linkin-parks-bassist/kestrel-pcb/3dmodels/neutrik-nmj4hcd2/NMJ4HCD2.png

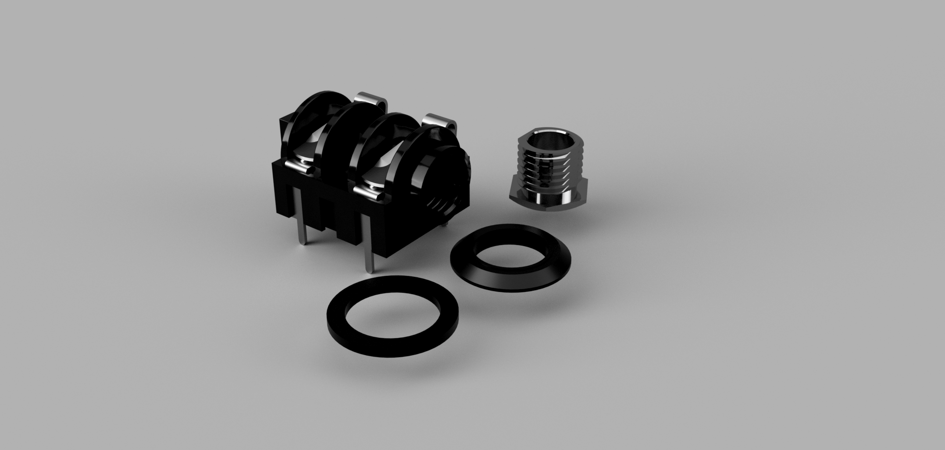
3dmodels/neutrik-nmj4hcd2/NMJ4HCD2.png
