linkin-parks-bassist/kestrel-pcb/rev-b/generated/pcb-adc-power.png

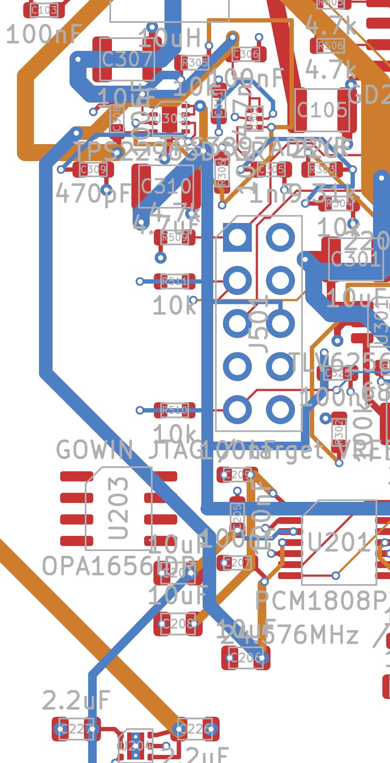
rev-b/generated/pcb-adc-power.png
