linkin-parks-bassist/kestrel-pcb/rev-b/generated/pcb-adc-support.png

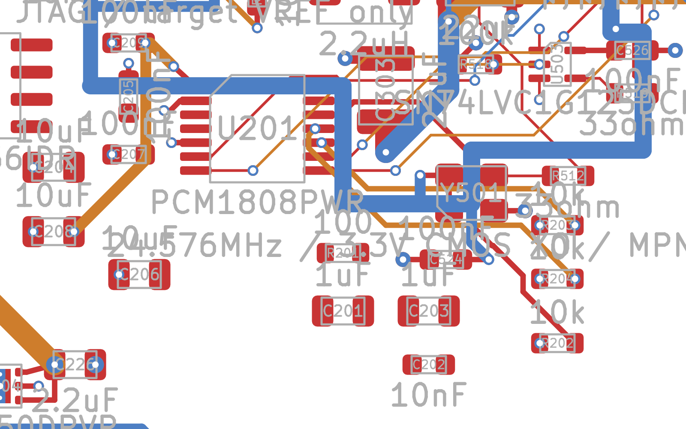
rev-b/generated/pcb-adc-support.png
