linkin-parks-bassist/kestrel-pcb/rev-b/generated/pcb-analogue-input.png

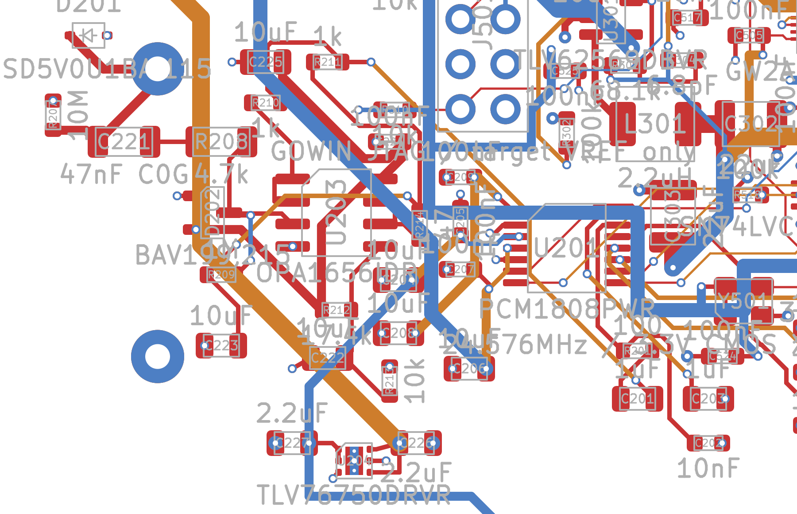
rev-b/generated/pcb-analogue-input.png
