linkin-parks-bassist/kestrel-pcb/rev-b/generated/pcb-analogue-output.png

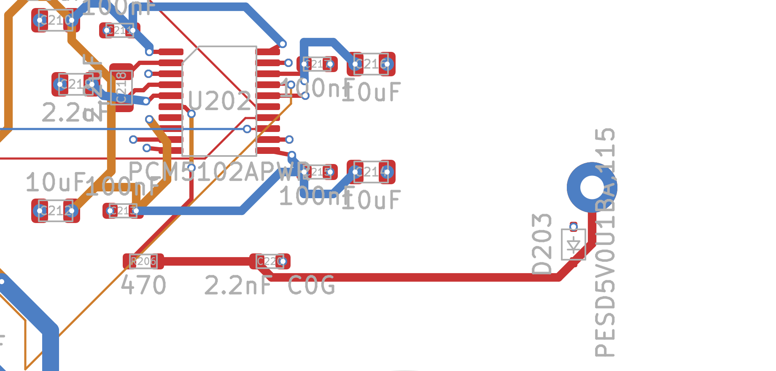
rev-b/generated/pcb-analogue-output.png
