linkin-parks-bassist/kestrel-pcb/rev-b/generated/pcb-analogue-power.png

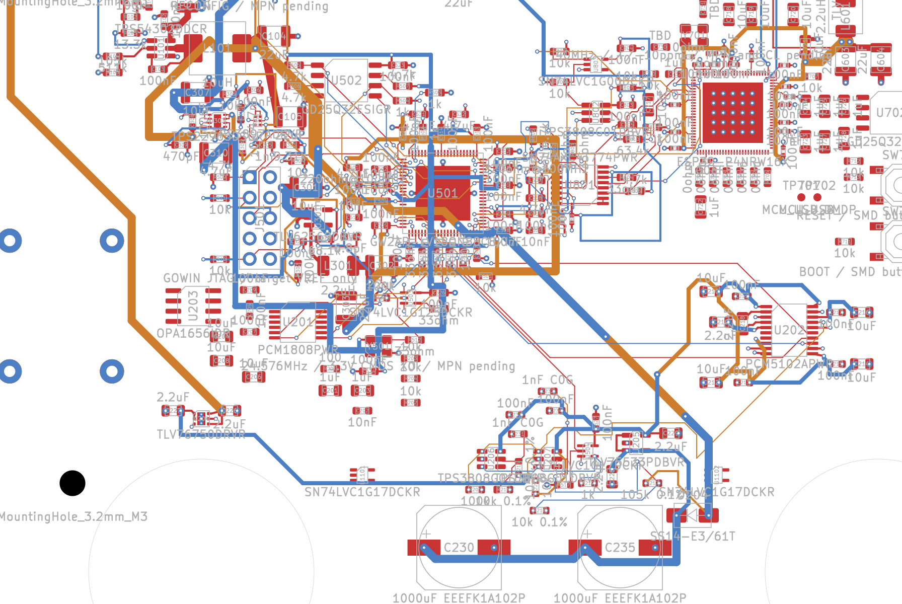
rev-b/generated/pcb-analogue-power.png
