linkin-parks-bassist/kestrel-pcb/rev-b/generated/pcb-audio-mute.png

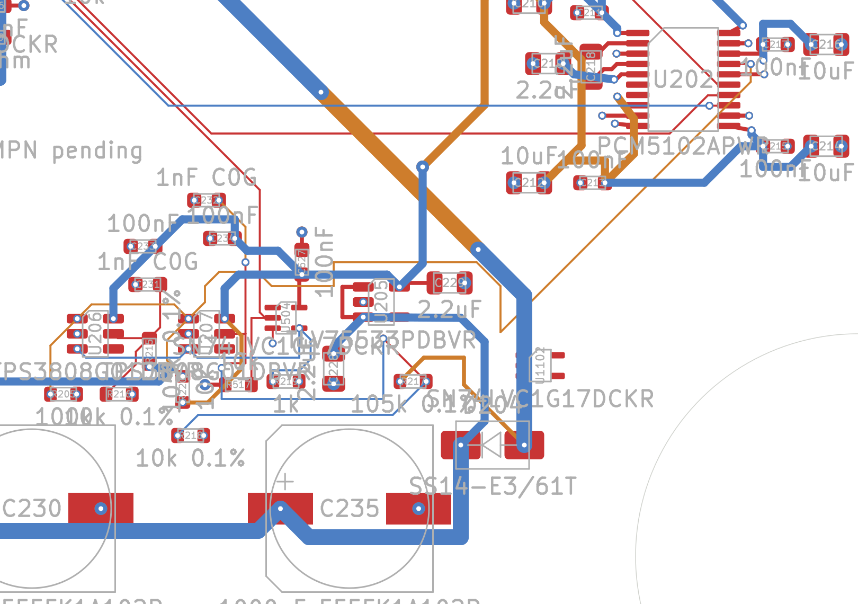
rev-b/generated/pcb-audio-mute.png
