linkin-parks-bassist/kestrel-pcb/rev-b/generated/pcb-backlight-pwm-escape.png

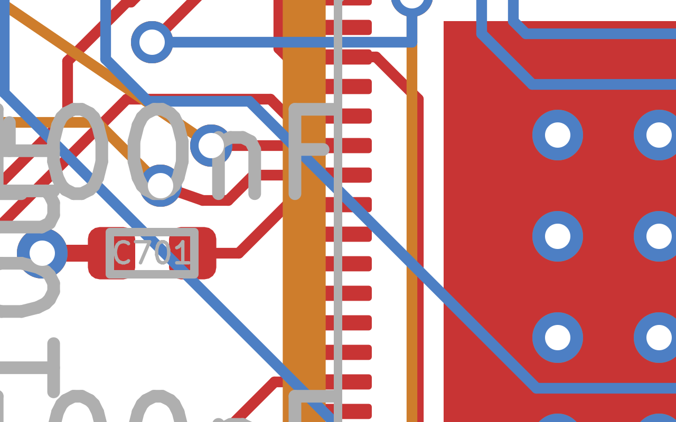
rev-b/generated/pcb-backlight-pwm-escape.png
