linkin-parks-bassist/kestrel-pcb/rev-b/generated/pcb-backlight-supply.png

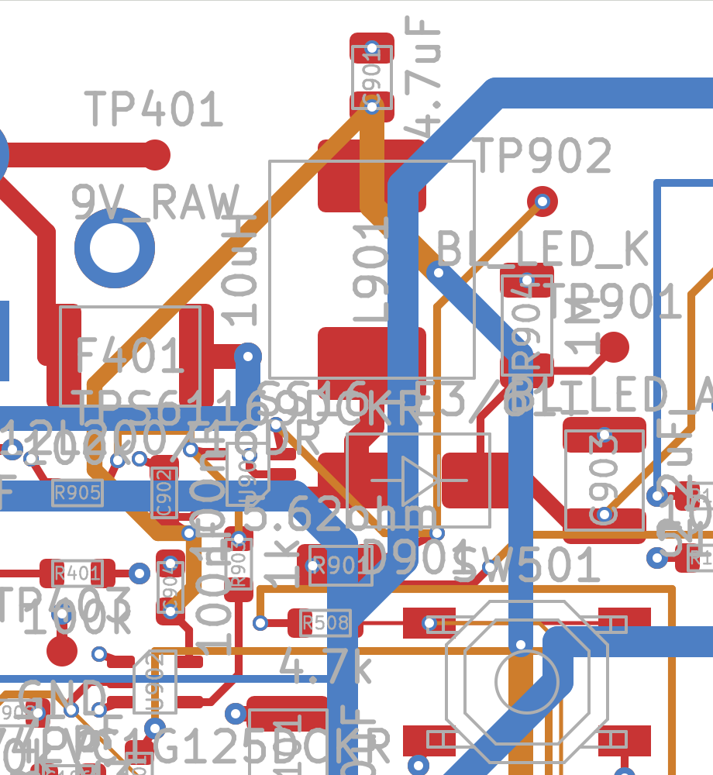
rev-b/generated/pcb-backlight-supply.png
