linkin-parks-bassist/kestrel-pcb/rev-b/generated/pcb-dac-support.png

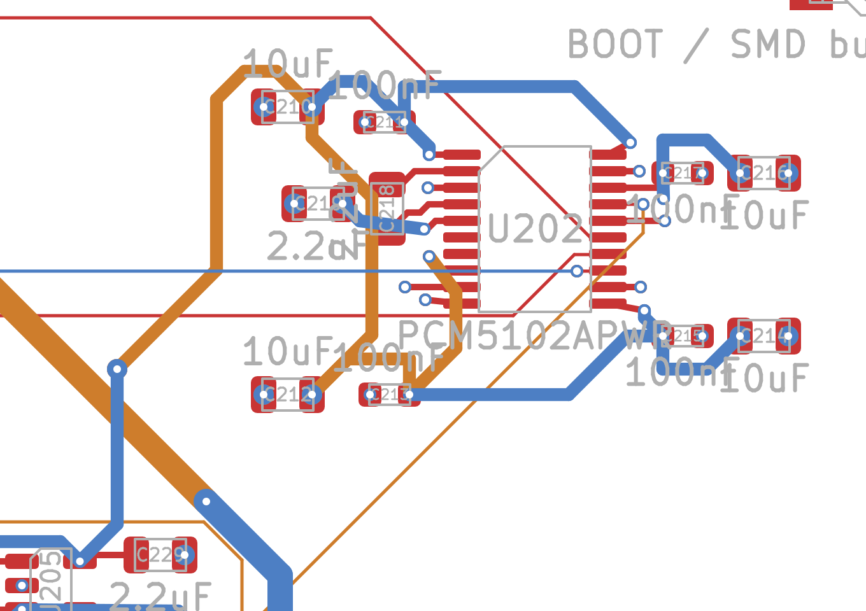
rev-b/generated/pcb-dac-support.png
