linkin-parks-bassist/kestrel-pcb/rev-b/generated/pcb-display-connector-supply.png

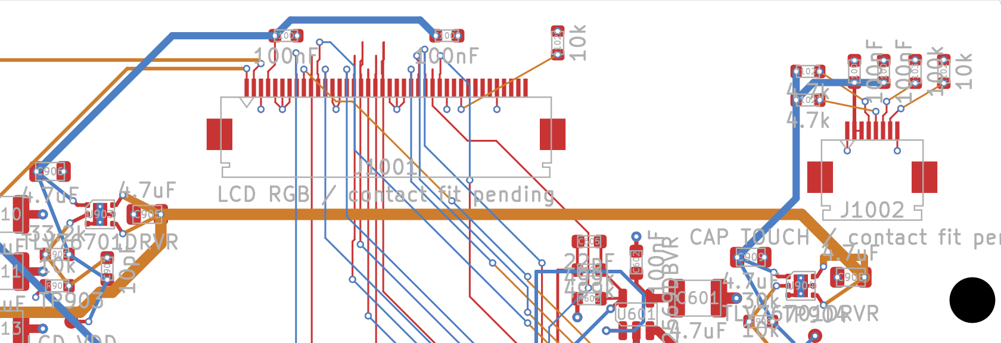
rev-b/generated/pcb-display-connector-supply.png
