linkin-parks-bassist/kestrel-pcb/rev-b/generated/pcb-display-feeds.png

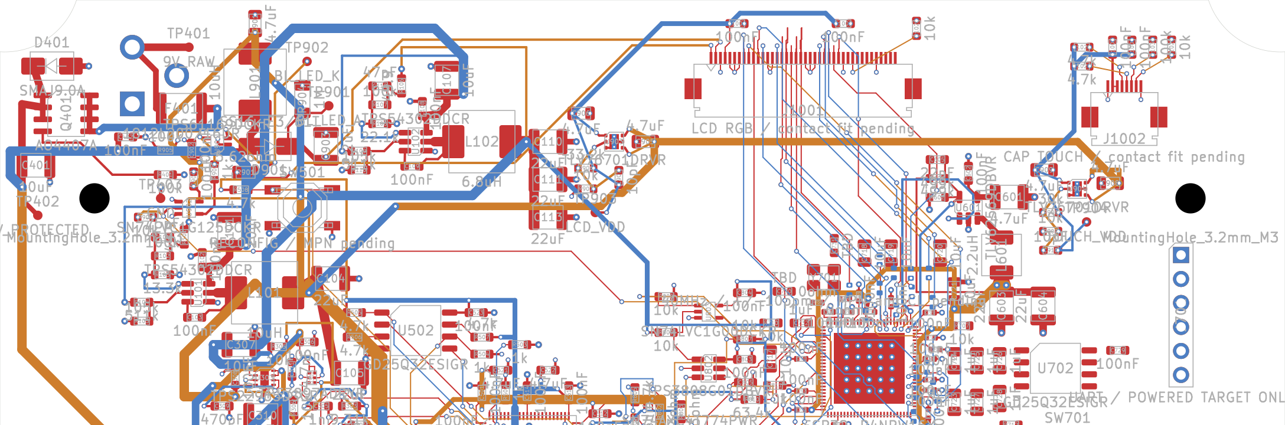
rev-b/generated/pcb-display-feeds.png
