linkin-parks-bassist/kestrel-pcb/rev-b/generated/pcb-display-led-fpc.png

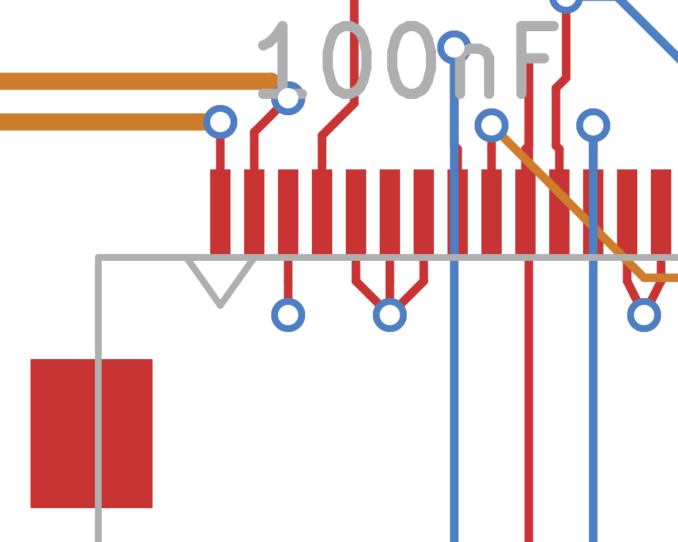
rev-b/generated/pcb-display-led-fpc.png
