linkin-parks-bassist/kestrel-pcb/rev-b/generated/pcb-display-rgb-damping.png

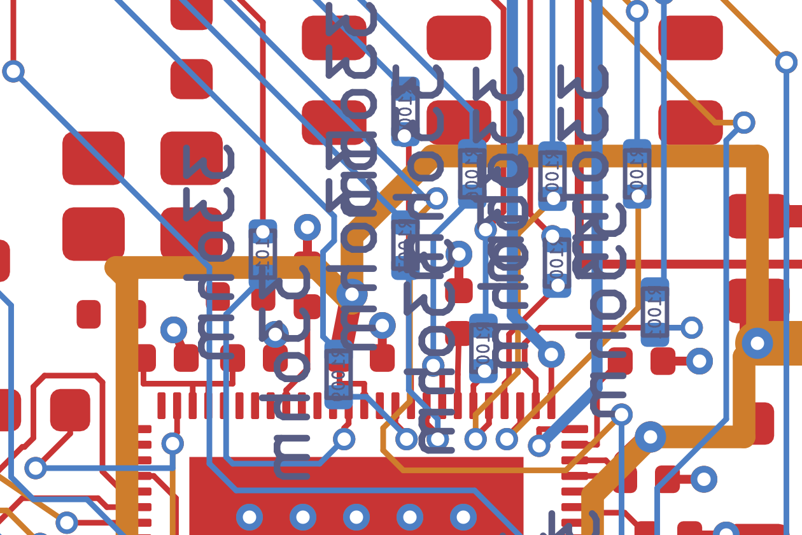
rev-b/generated/pcb-display-rgb-damping.png
