linkin-parks-bassist/kestrel-pcb/rev-b/generated/pcb-display-rgb-output-escape.png

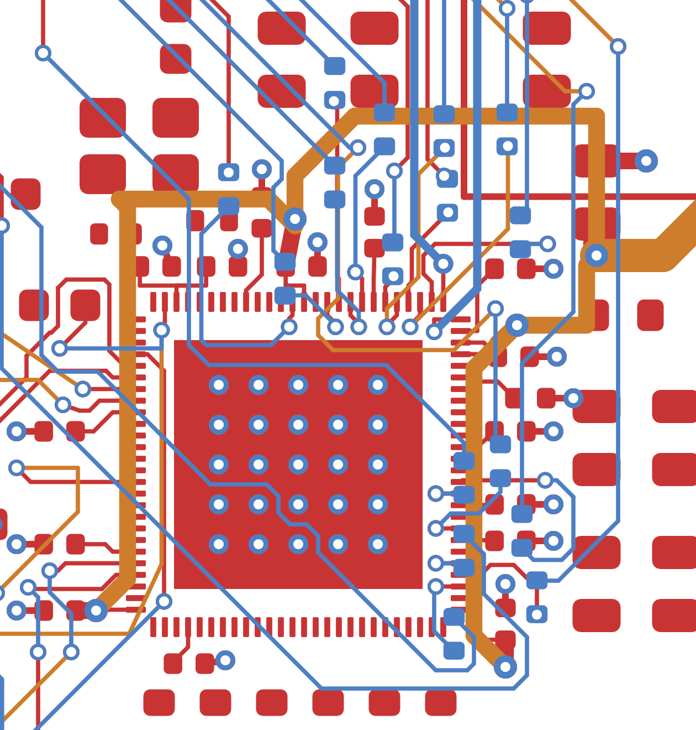
rev-b/generated/pcb-display-rgb-output-escape.png
