linkin-parks-bassist/kestrel-pcb/rev-b/generated/pcb-display-rgb-output.png

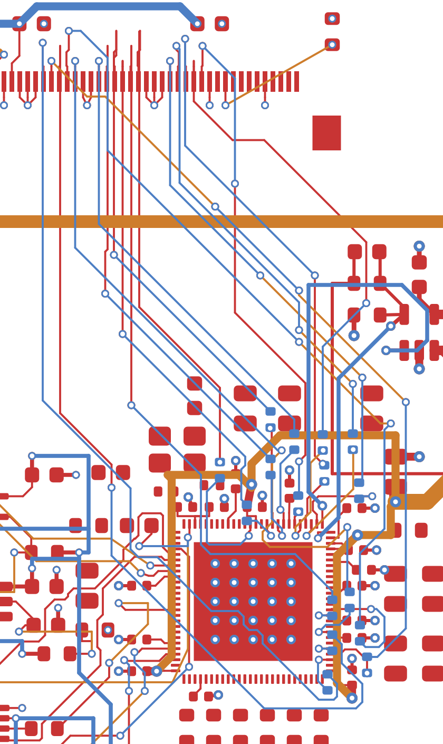
rev-b/generated/pcb-display-rgb-output.png
