linkin-parks-bassist/kestrel-pcb/rev-b/generated/pcb-display-rgb-right.png

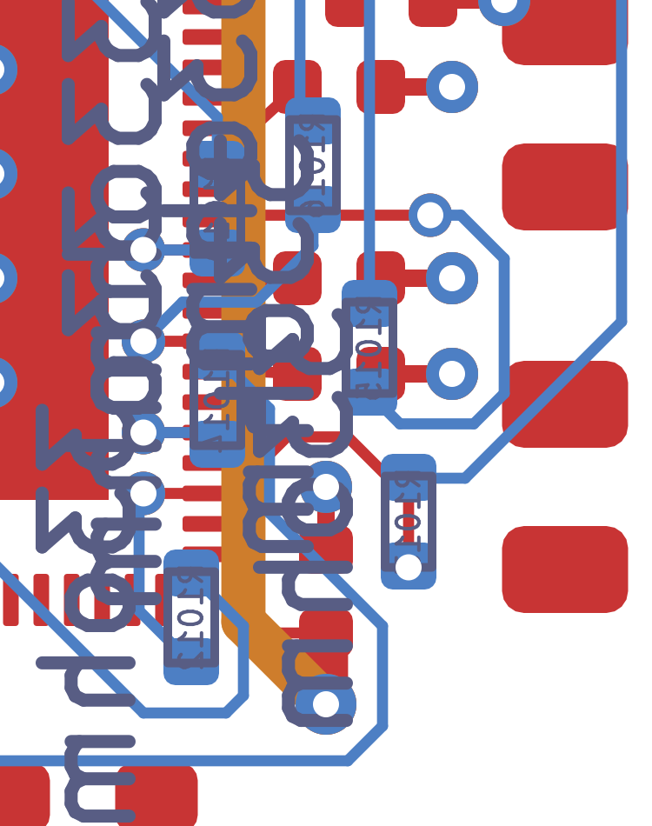
rev-b/generated/pcb-display-rgb-right.png
