linkin-parks-bassist/kestrel-pcb/rev-b/generated/pcb-footswitch-left.png

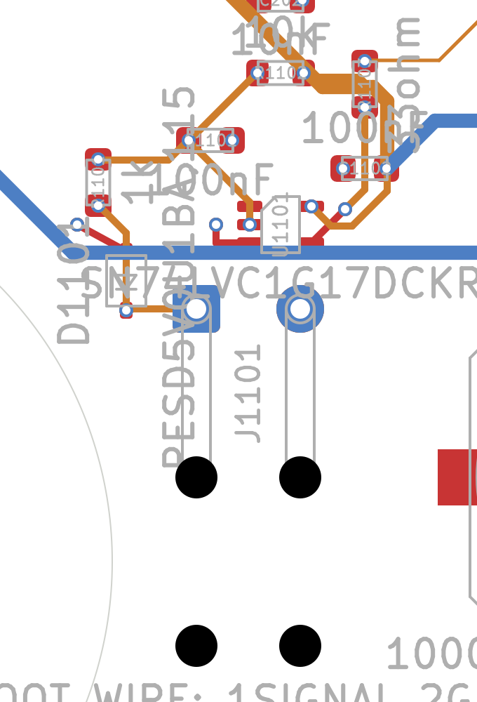
rev-b/generated/pcb-footswitch-left.png
