linkin-parks-bassist/kestrel-pcb/rev-b/generated/pcb-footswitch-mcu.png

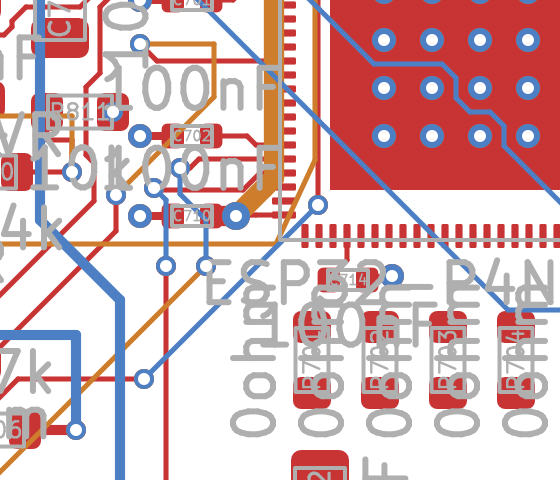
rev-b/generated/pcb-footswitch-mcu.png
