linkin-parks-bassist/kestrel-pcb/rev-b/generated/pcb-footswitch-placement.png

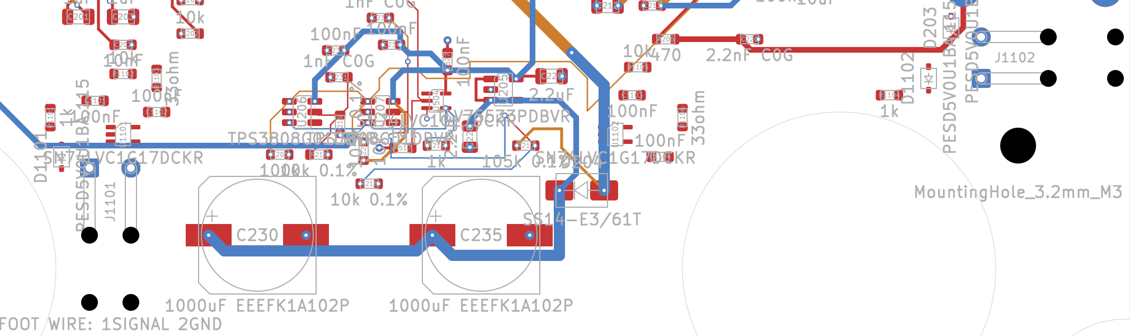
rev-b/generated/pcb-footswitch-placement.png
