linkin-parks-bassist/kestrel-pcb/rev-b/generated/pcb-footswitch-right.png

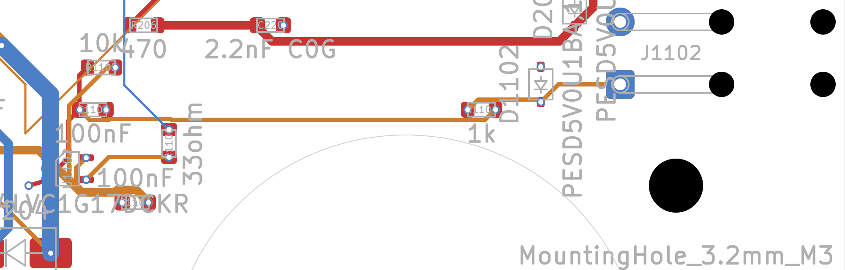
rev-b/generated/pcb-footswitch-right.png
