linkin-parks-bassist/kestrel-pcb/rev-b/generated/pcb-fpga-audio.png

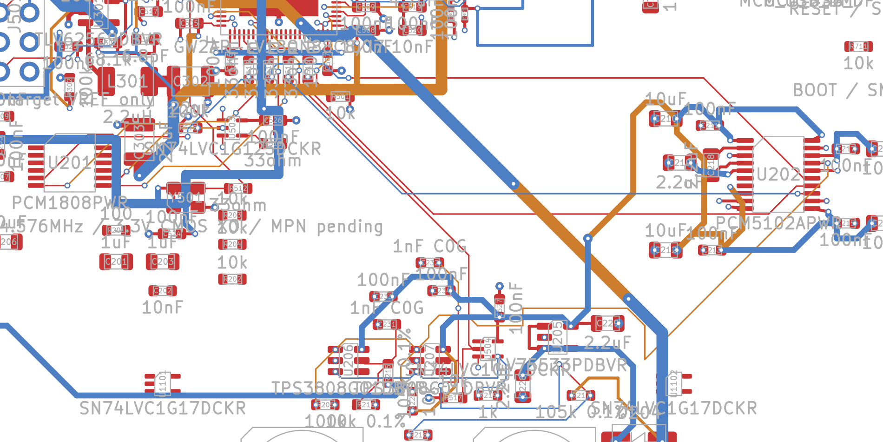
rev-b/generated/pcb-fpga-audio.png
