linkin-parks-bassist/kestrel-pcb/rev-b/generated/pcb-fpga-core-distribution.png

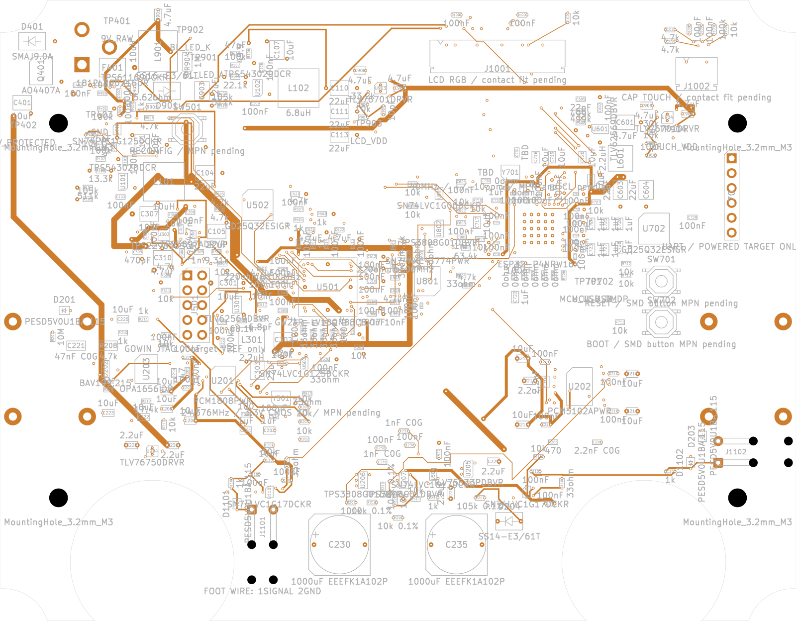
rev-b/generated/pcb-fpga-core-distribution.png
