linkin-parks-bassist/kestrel-pcb/rev-b/generated/pcb-fpga-flash.png

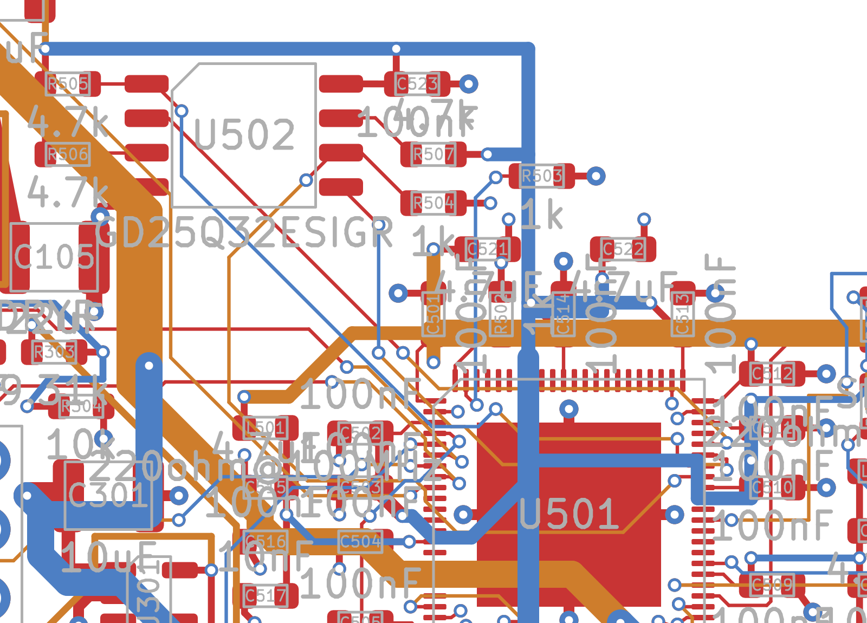
rev-b/generated/pcb-fpga-flash.png
