linkin-parks-bassist/kestrel-pcb/rev-b/generated/pcb-fpga-io-distribution.png

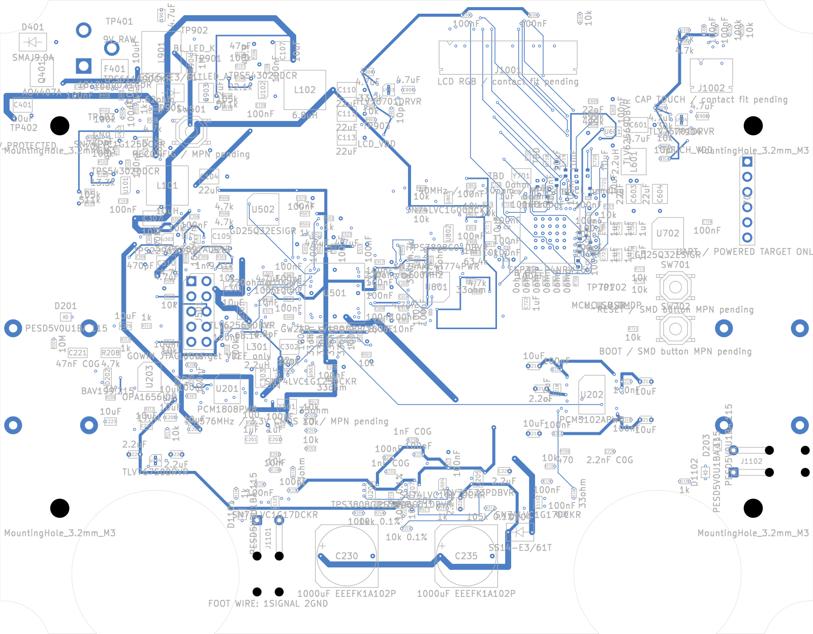
rev-b/generated/pcb-fpga-io-distribution.png
