linkin-parks-bassist/kestrel-pcb/rev-b/generated/pcb-fpga-service.png

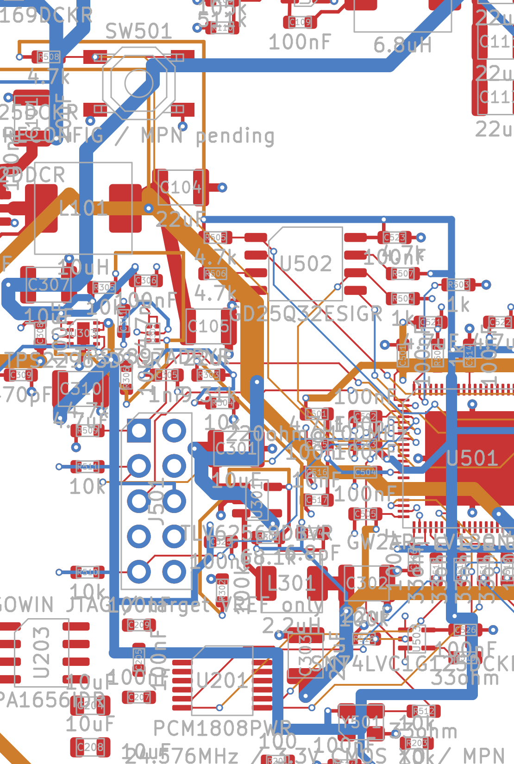
rev-b/generated/pcb-fpga-service.png
