linkin-parks-bassist/kestrel-pcb/rev-b/generated/pcb-ground.png

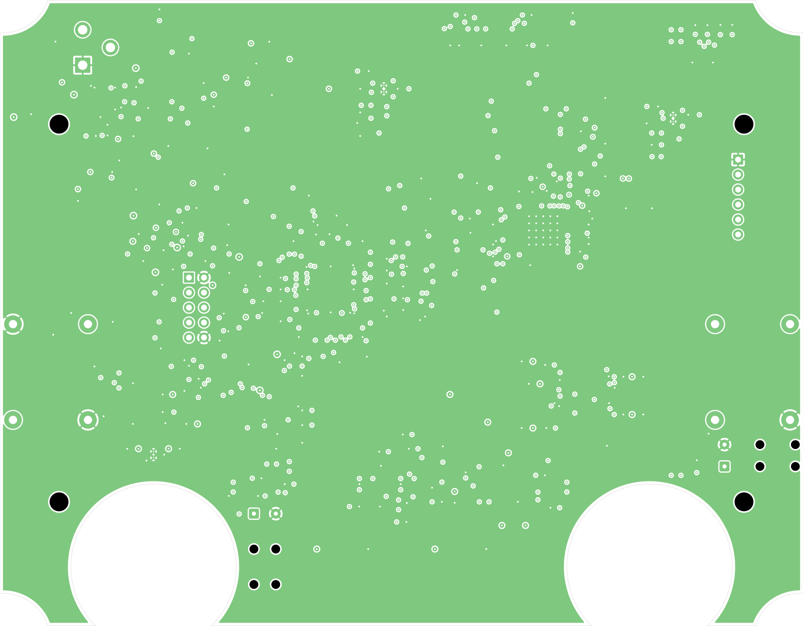
rev-b/generated/pcb-ground.png
