linkin-parks-bassist/kestrel-pcb/rev-b/generated/pcb-hp-distribution.png

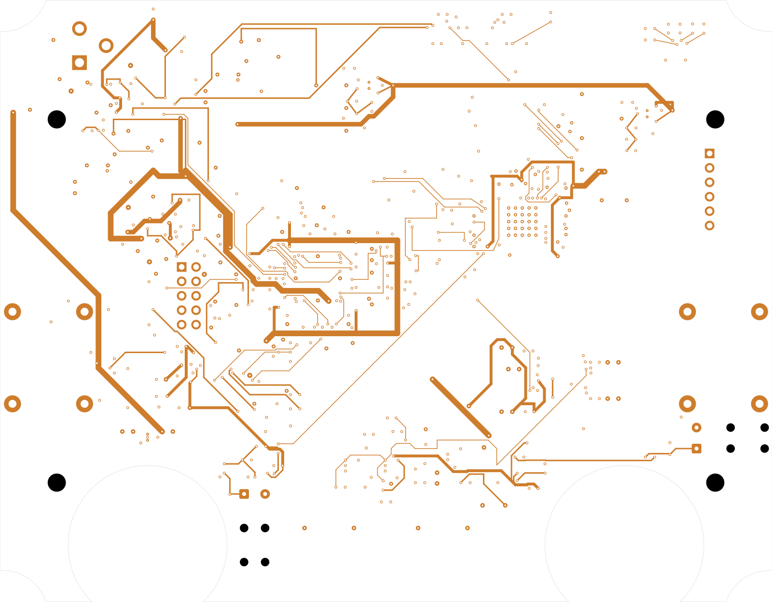
rev-b/generated/pcb-hp-distribution.png
