linkin-parks-bassist/kestrel-pcb/rev-b/generated/pcb-input-underside.png

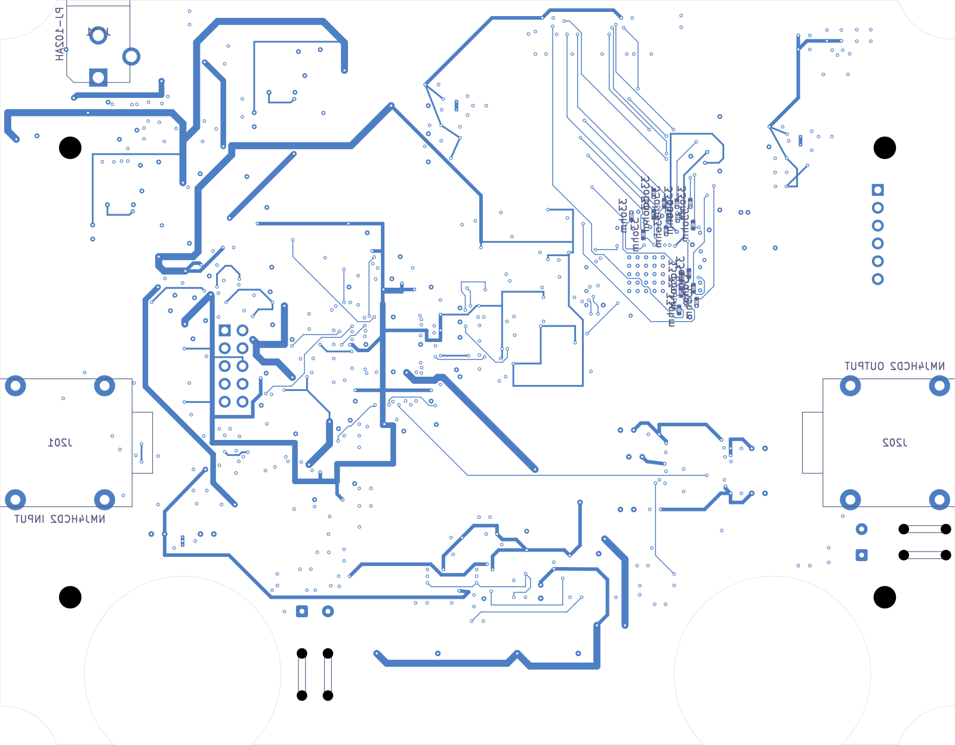
rev-b/generated/pcb-input-underside.png
