linkin-parks-bassist/kestrel-pcb/rev-b/generated/pcb-lcd-connector.png

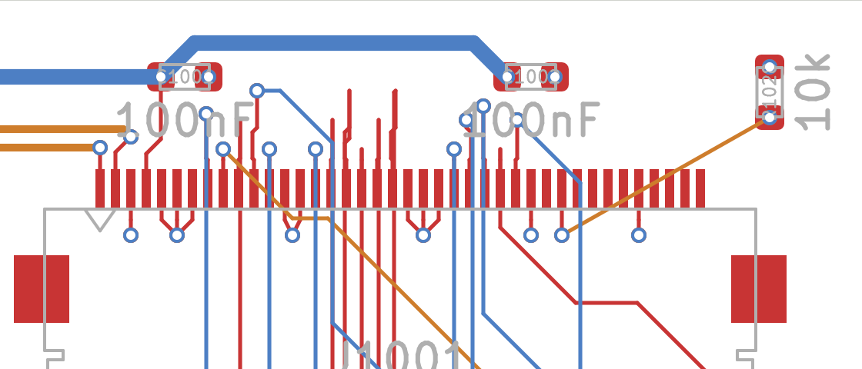
rev-b/generated/pcb-lcd-connector.png
