linkin-parks-bassist/kestrel-pcb/rev-b/generated/pcb-lcd-supply.png

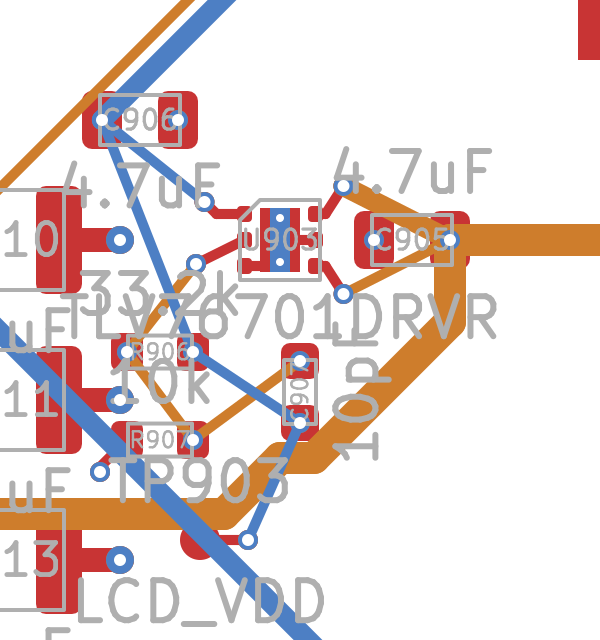
rev-b/generated/pcb-lcd-supply.png
