linkin-parks-bassist/kestrel-pcb/rev-b/generated/pcb-placement.png

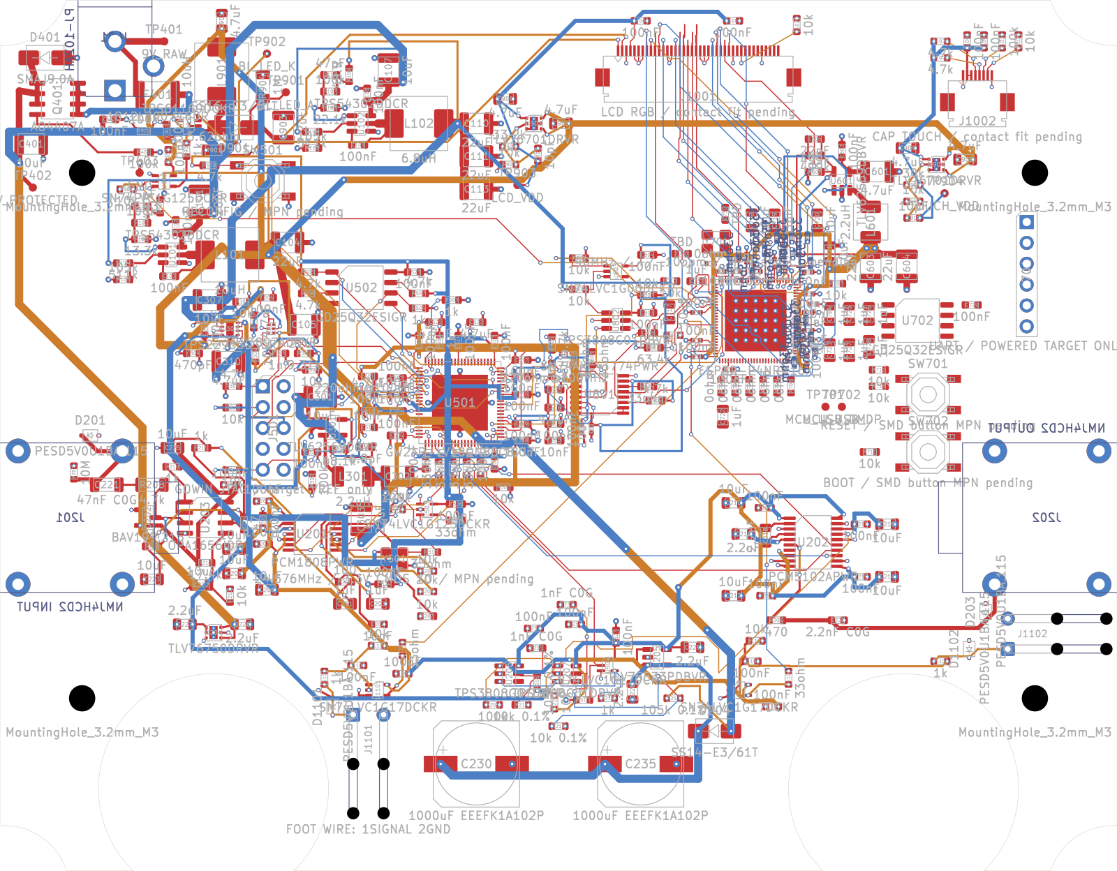
rev-b/generated/pcb-placement.png
