linkin-parks-bassist/kestrel-pcb/rev-b/generated/pcb-touch-connector.png

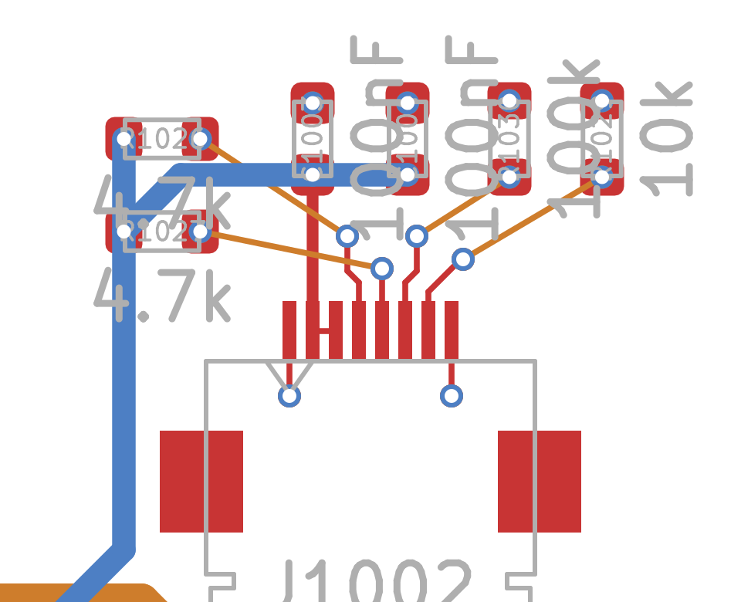
rev-b/generated/pcb-touch-connector.png
