linkin-parks-bassist/kestrel-pcb/rev-b/generated/pcb-touch-supply.png

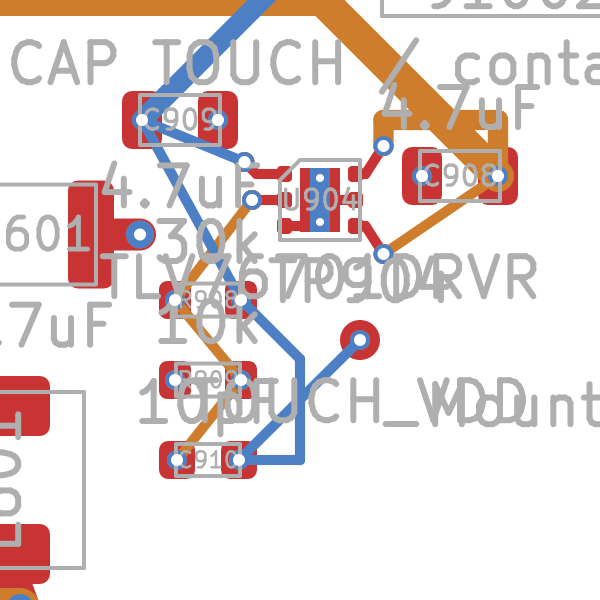
rev-b/generated/pcb-touch-supply.png
