linkin-parks-bassist/kestrel-pcb/rev-b/generated/review/esp32-p4-footprint.png

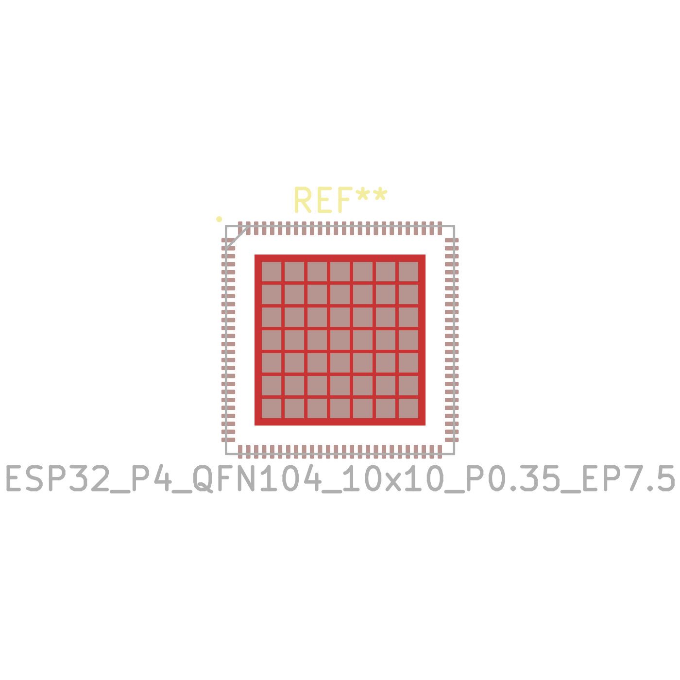
rev-b/generated/review/esp32-p4-footprint.png
