linkin-parks-bassist/kestrel-pcb/rev-b/generated/review/fpga-qn88-footprint.png

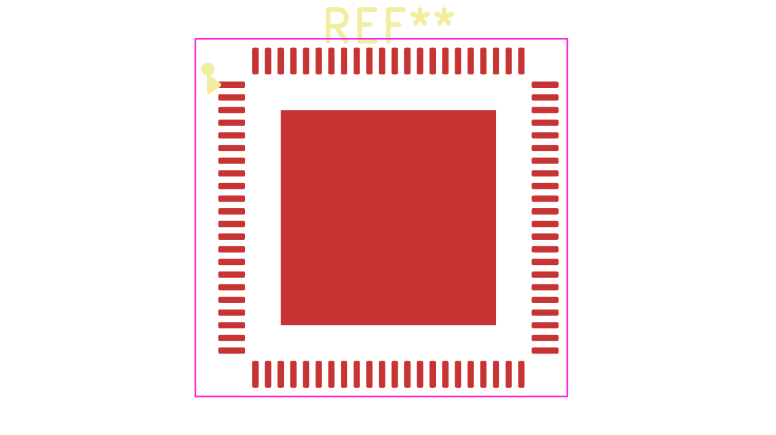
rev-b/generated/review/fpga-qn88-footprint.png
