linkin-parks-bassist/kestrel-pcb/rev-b/generated/review/kestrel-revb-Backlight and display supplies.png

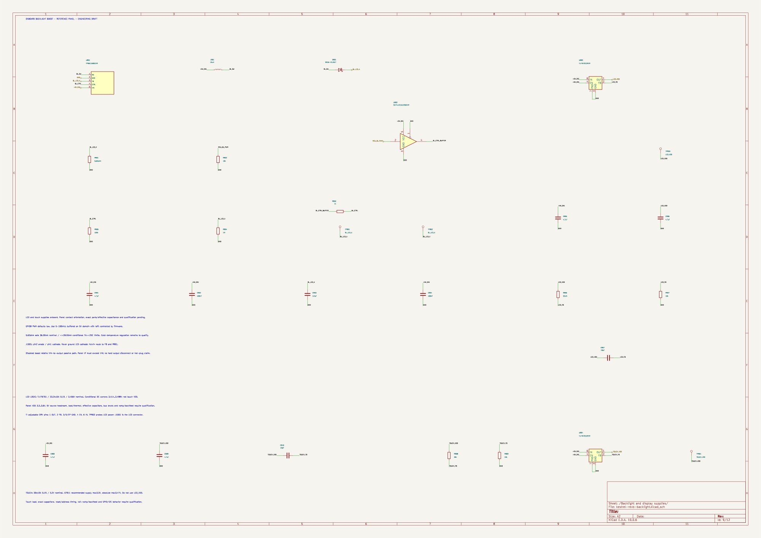
rev-b/generated/review/kestrel-revb-Backlight and display supplies.png
