linkin-parks-bassist/kestrel-pcb/rev-b/generated/review/kestrel-revb-Bare ESP32-P4 support.png

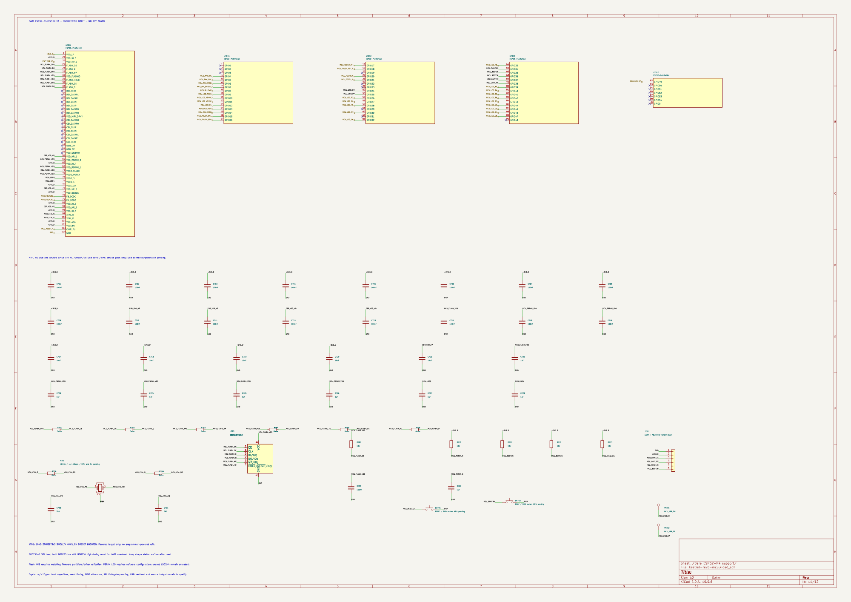
rev-b/generated/review/kestrel-revb-Bare ESP32-P4 support.png
