linkin-parks-bassist/kestrel-pcb/rev-b/generated/review/kestrel-revb-Bare GW2AR-18 support.png

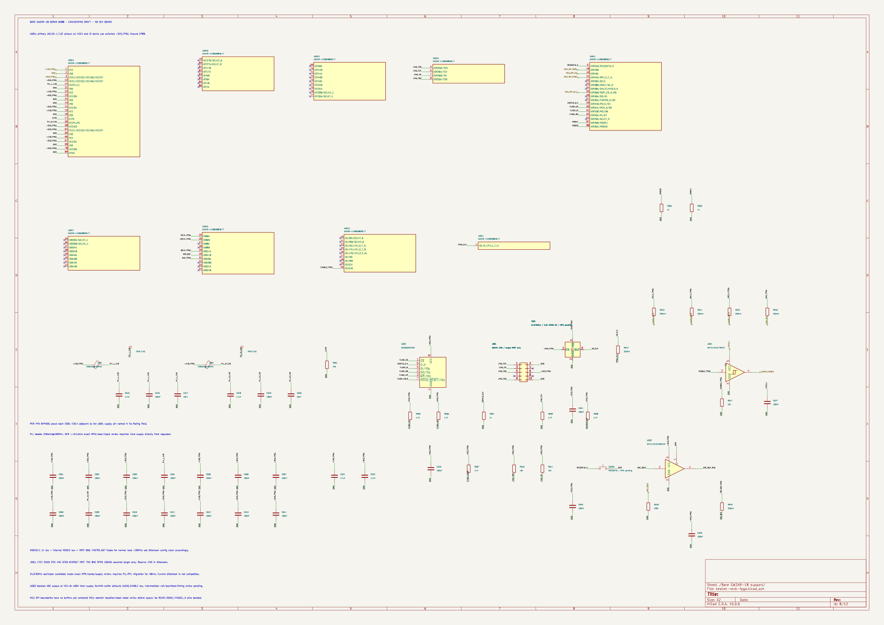
rev-b/generated/review/kestrel-revb-Bare GW2AR-18 support.png
