linkin-parks-bassist/kestrel-pcb/rev-b/generated/review/kestrel-revb-Centre-negative 9 V input.png

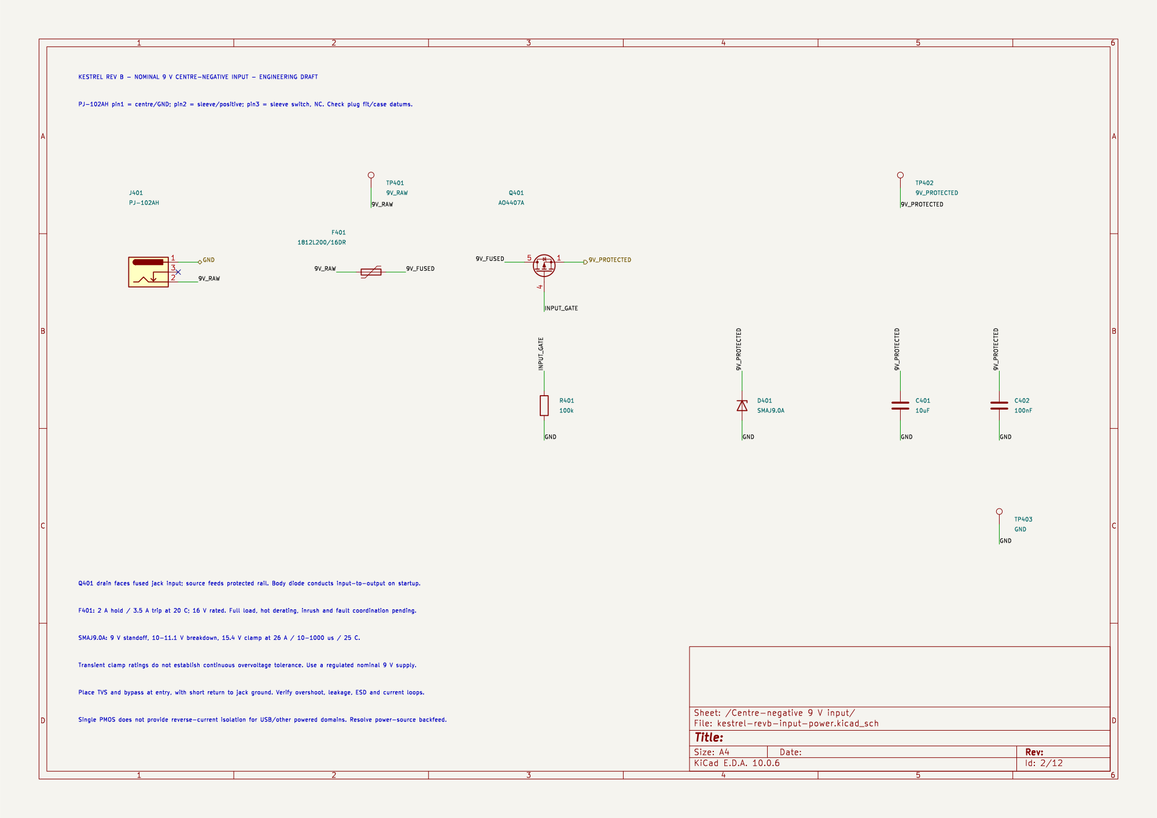
rev-b/generated/review/kestrel-revb-Centre-negative 9 V input.png
