linkin-parks-bassist/kestrel-pcb/rev-b/generated/review/kestrel-revb-FPGA core and I_O sequencing.png

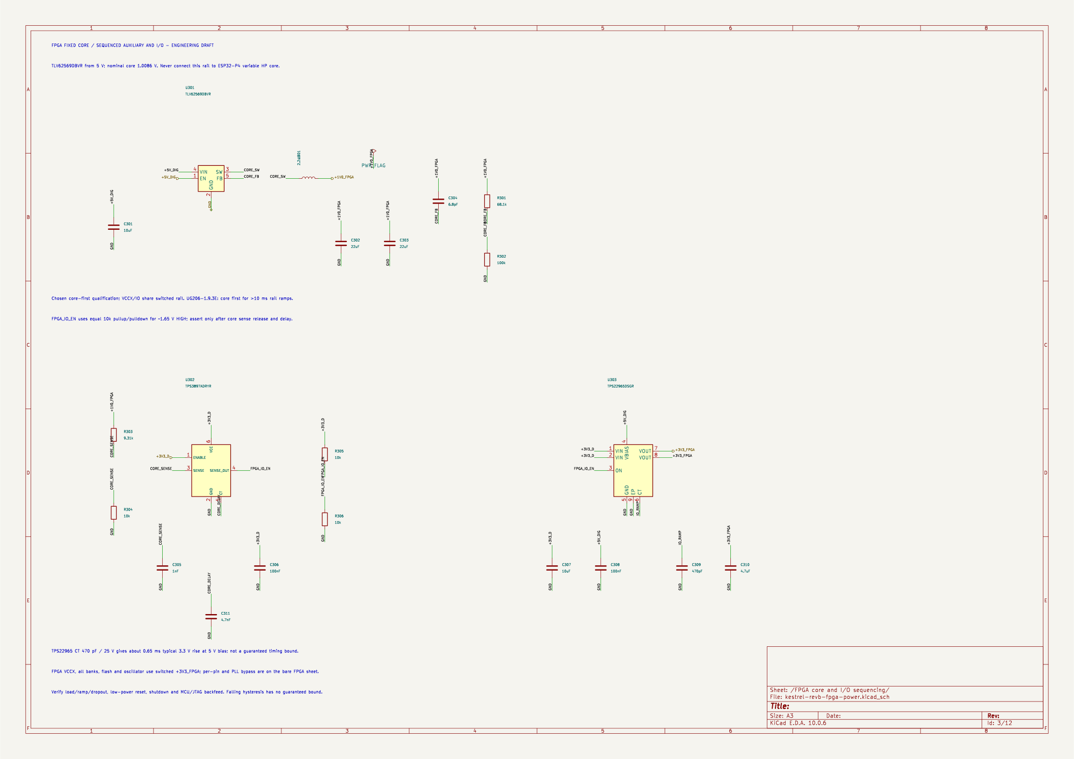
rev-b/generated/review/kestrel-revb-FPGA core and I_O sequencing.png
