linkin-parks-bassist/kestrel-pcb/rev-b/generated/review/kestrel-revb-Onboard 5 V and 3.3 V bucks.png

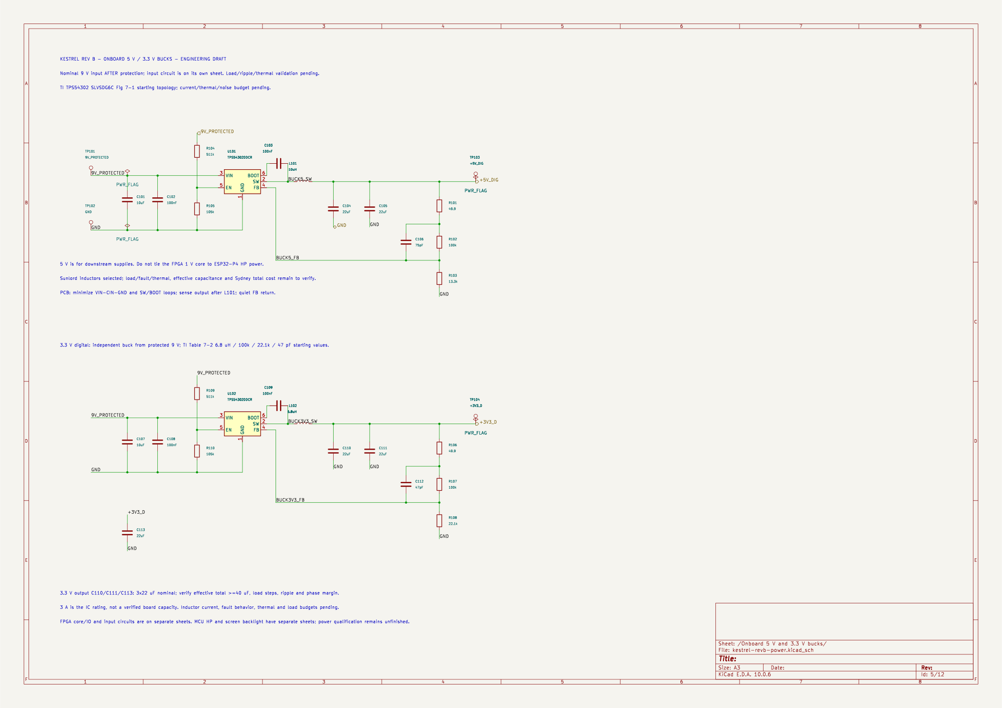
rev-b/generated/review/kestrel-revb-Onboard 5 V and 3.3 V bucks.png
