linkin-parks-bassist/kestrel-pcb/rev-b/generated/review/kestrel-revb-P4 controlled HP regulator.png

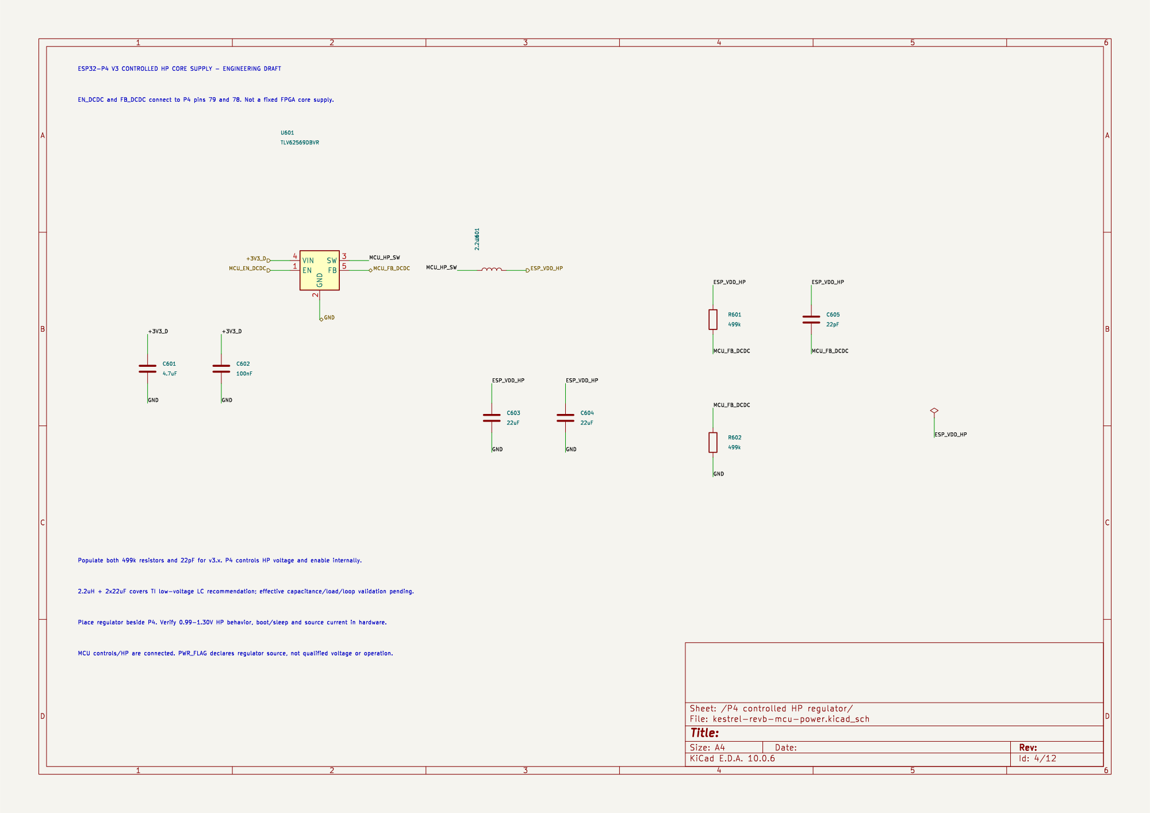
rev-b/generated/review/kestrel-revb-P4 controlled HP regulator.png
