linkin-parks-bassist/kestrel-pcb/rev-b/generated/review/kestrel-revb-Power-domain SPI isolation.png

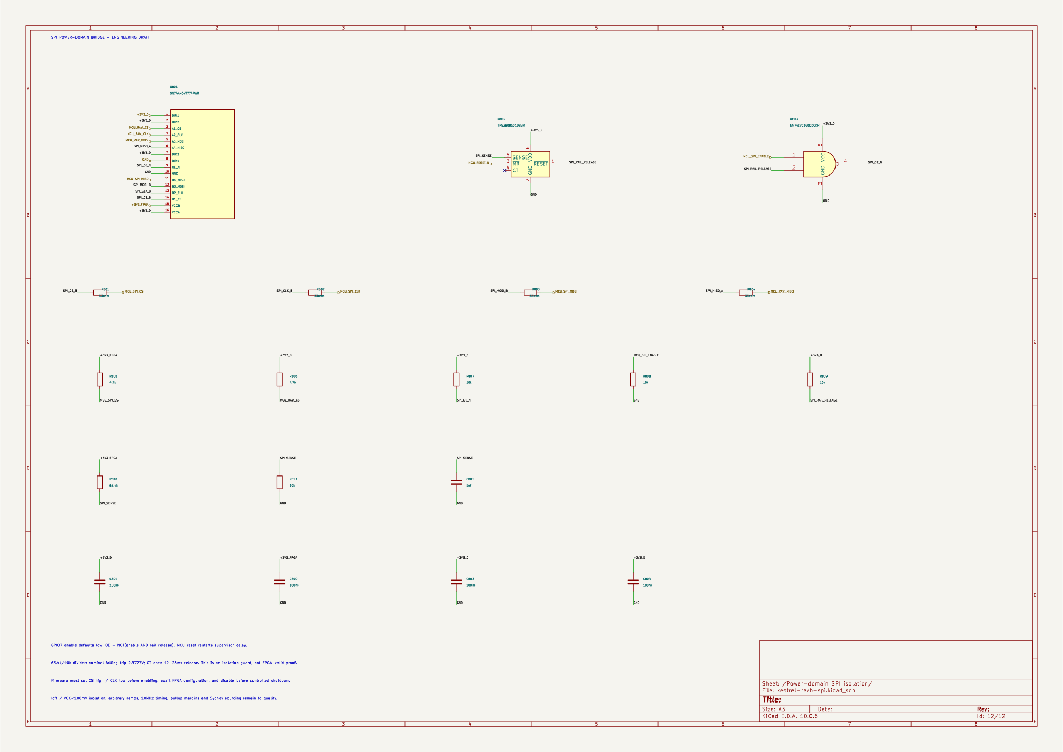
rev-b/generated/review/kestrel-revb-Power-domain SPI isolation.png
