linkin-parks-bassist/kestrel-pcb/rev-b/generated/review/kestrel-revb-RGB565 and capacitive touch.png

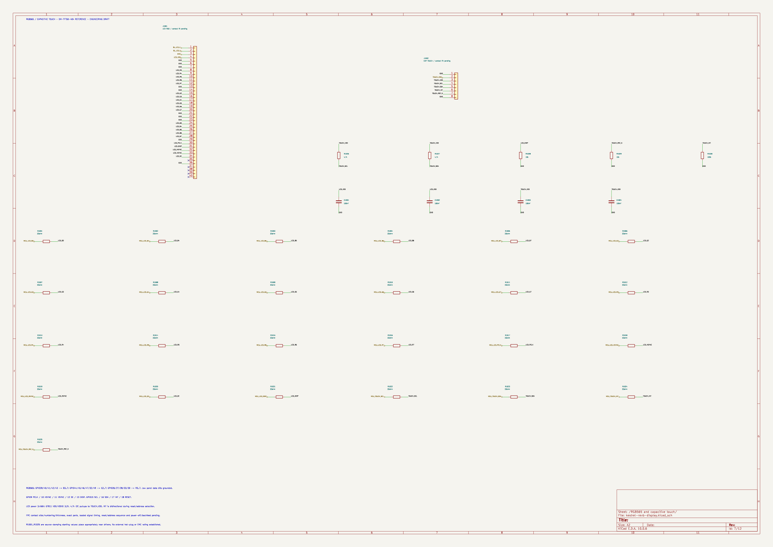
rev-b/generated/review/kestrel-revb-RGB565 and capacitive touch.png
