linkin-parks-bassist/kestrel-pcb/rev-b/generated/review/kestrel-revb-Two momentary footswitch inputs.png

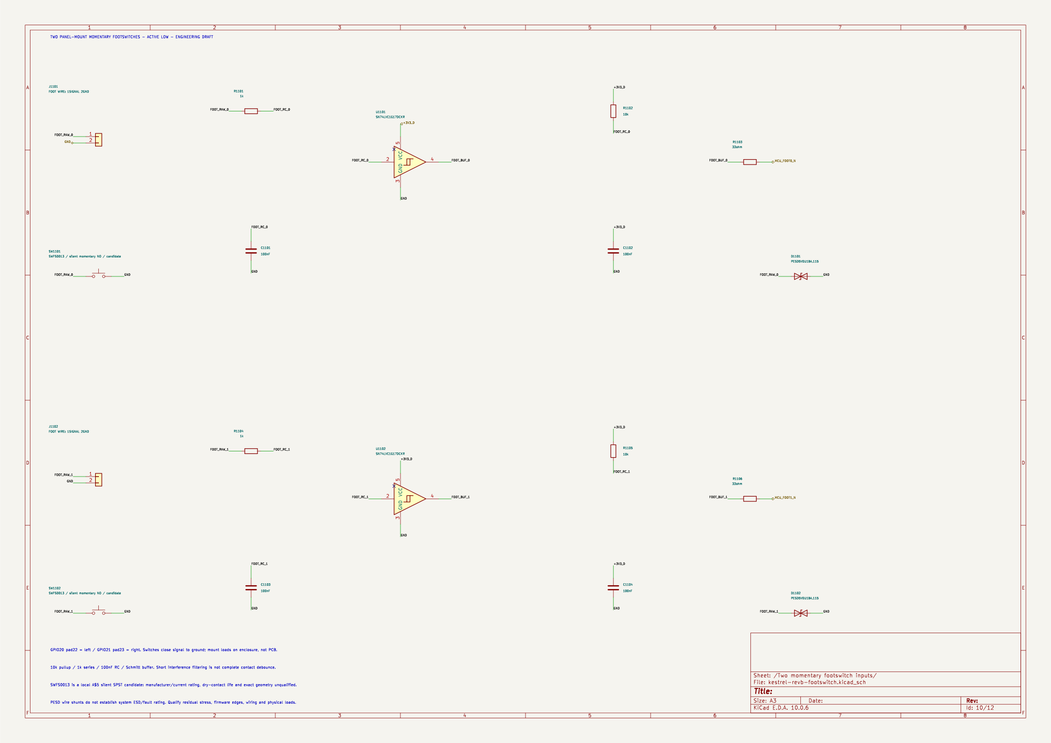
rev-b/generated/review/kestrel-revb-Two momentary footswitch inputs.png
