linkin-parks-bassist/kestrel-pcb/rev-b/generated/review/kestrel-revb.png

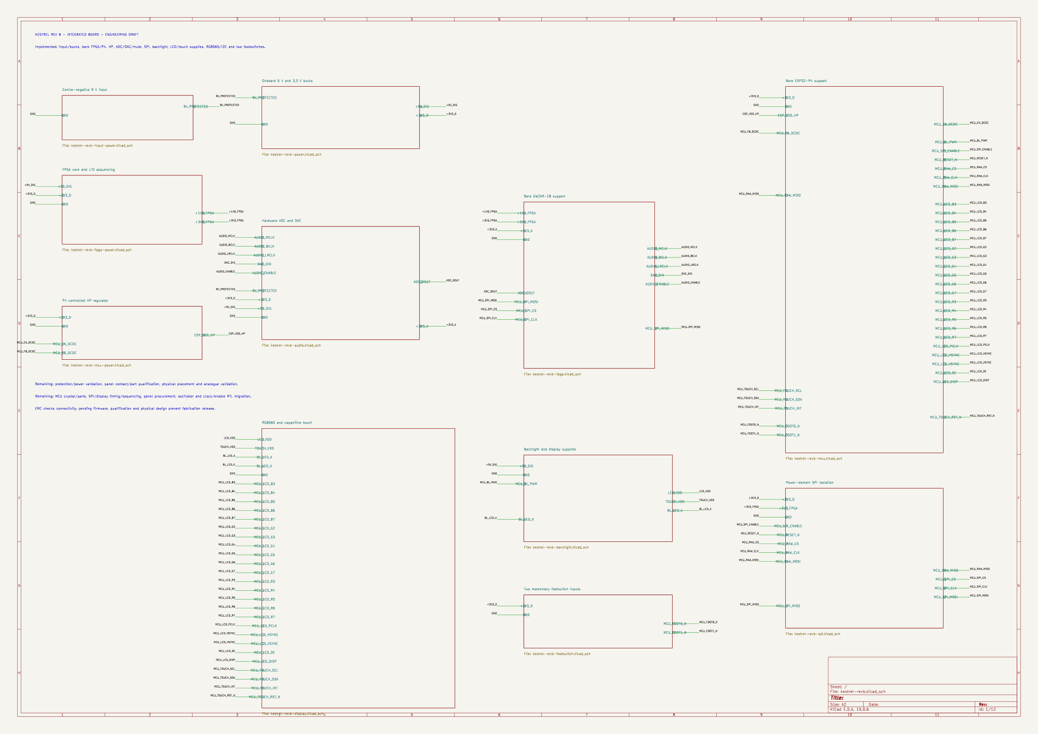
rev-b/generated/review/kestrel-revb.png
