linkin-parks-bassist/kestrel-pcb/rev-b/generated/upper-shell.png

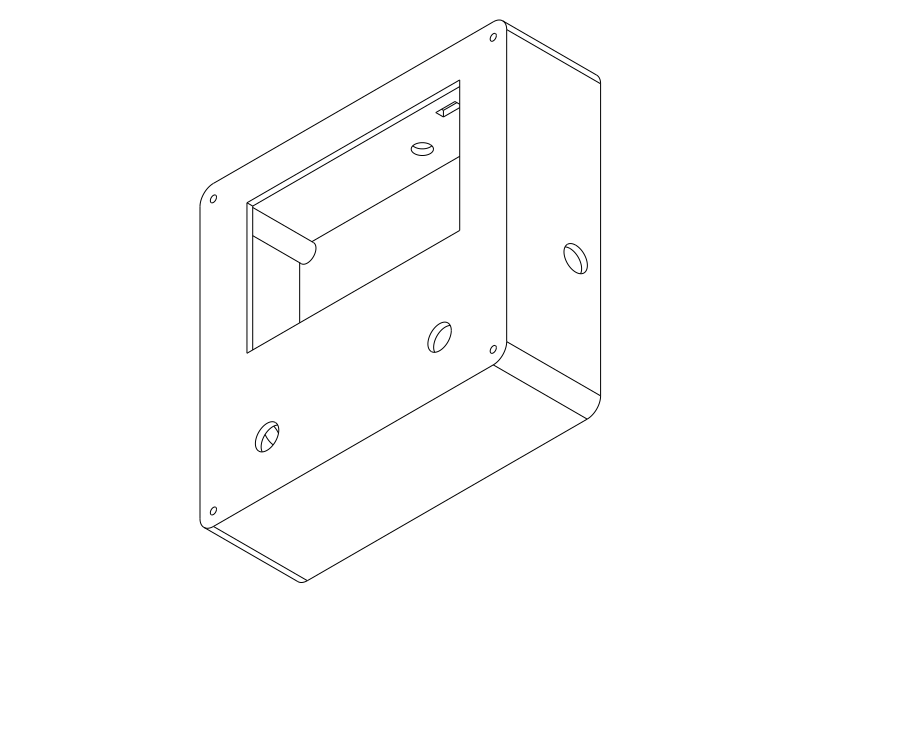
rev-b/generated/upper-shell.png
